jheyer159/leaf-case/images/BBB_Pin_Label_2x4_preview_featured.jpg

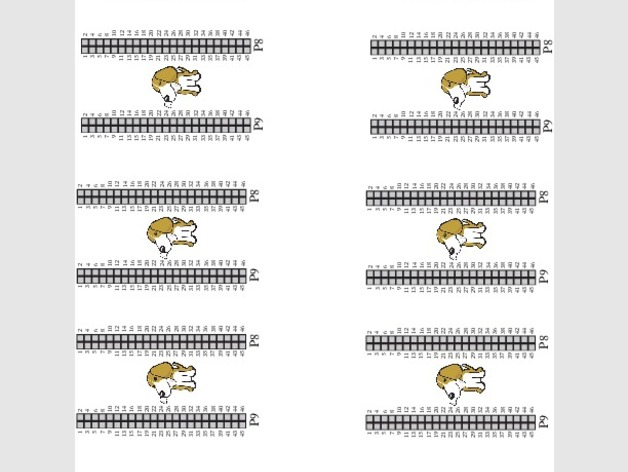
images/BBB_Pin_Label_2x4_preview_featured.jpg
