jheyer159/leaf-case/images/BBB_Slim_End_View_preview_featured.jpg

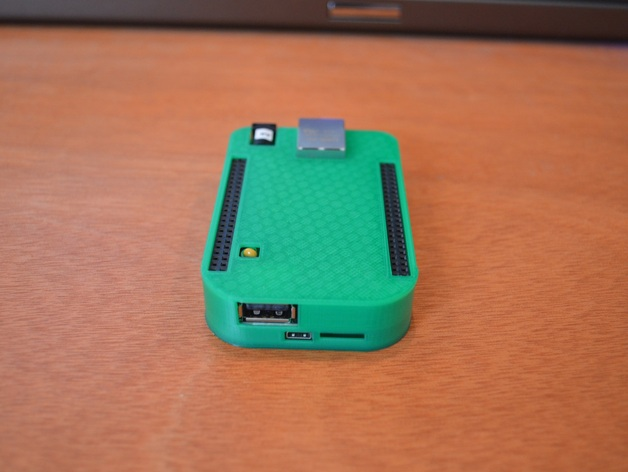
images/BBB_Slim_End_View_preview_featured.jpg
