jheyer159/leaf-case/images/BBB_Slim_Label_Sheet_preview_featured.jpg

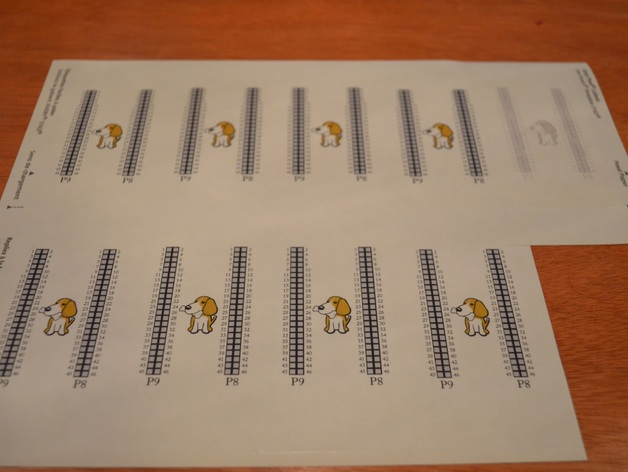
images/BBB_Slim_Label_Sheet_preview_featured.jpg
