jheyer159/leaf-case/images/BBB_Slim_Top_View_preview_featured.jpg

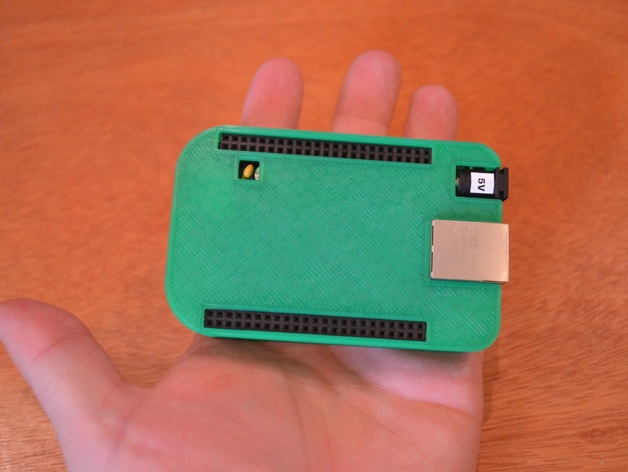
images/BBB_Slim_Top_View_preview_featured.jpg
