jheyer159/leaf-case/images/BBB_SlimCase_v2_Lid_preview_featured.jpg

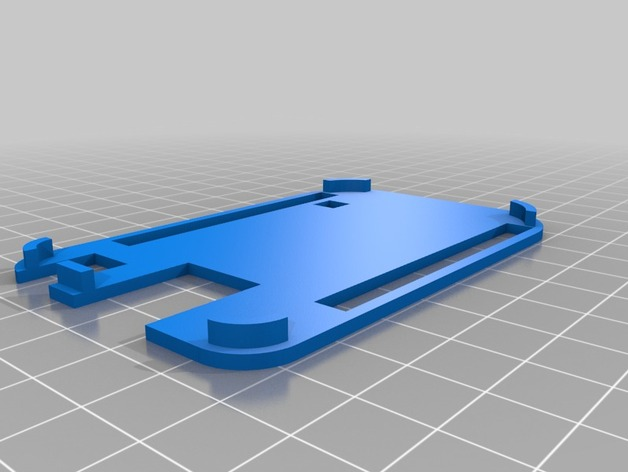
images/BBB_SlimCase_v2_Lid_preview_featured.jpg
